Aetriq/CEG491X-Capstone/model/Prototype 3 (v1.0)/TPU Rear Bumper.stl

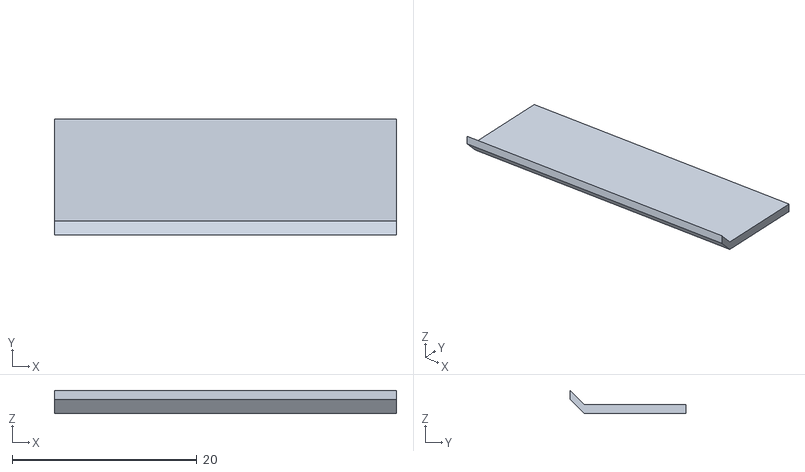
[picture p27: CAD file, 2026-04-08]
model/Prototype 3 (v1.0)/TPU Rear Bumper.stl
37.0 x 12.5 x 2.50
