Aetriq/CEG491X-Capstone/model/Prototype 3 (v1.0)/TPU Side Corner Bumper.stl

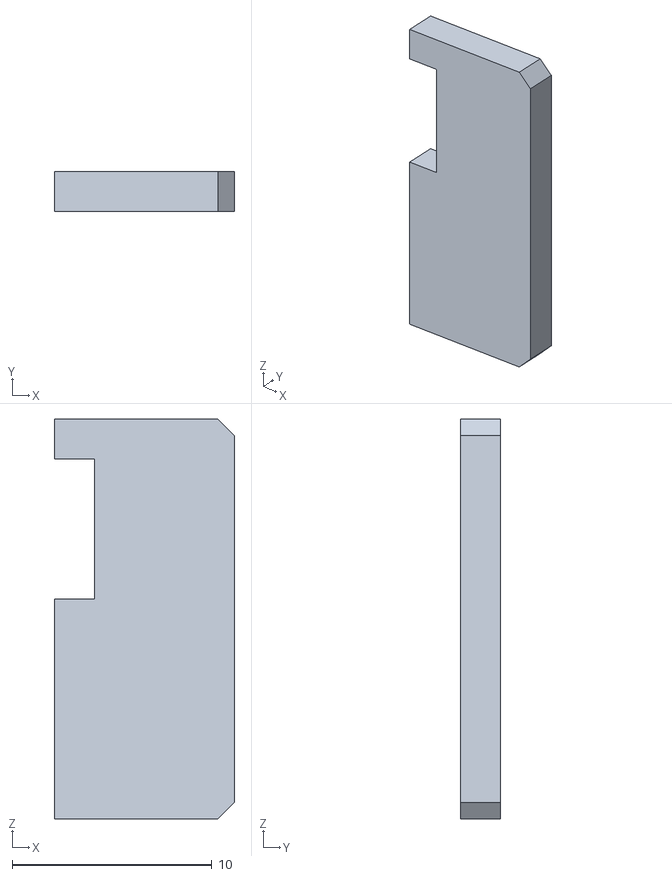
[picture p28: CAD file, 2026-04-08]
model/Prototype 3 (v1.0)/TPU Side Corner Bumper.stl
9.00 x 2.00 x 20.0
