Aetriq/CEG491X-Capstone/model/Prototype 3 (v1.0)/TPU Front Bumper.stl

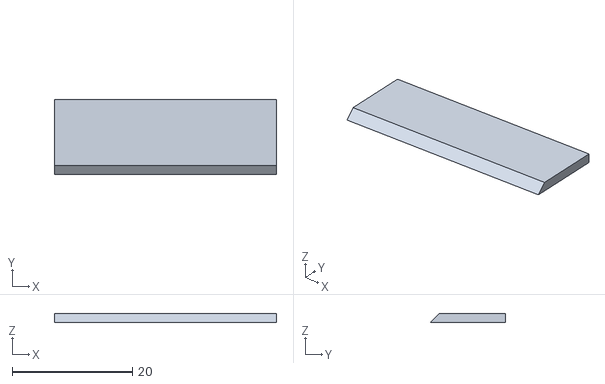
[picture p29: CAD file, 2026-04-08]
model/Prototype 3 (v1.0)/TPU Front Bumper.stl
37.0 x 12.5 x 1.50
